TAU-Robotics/ArduMotorControl/Photos/20200909_112209.jpg

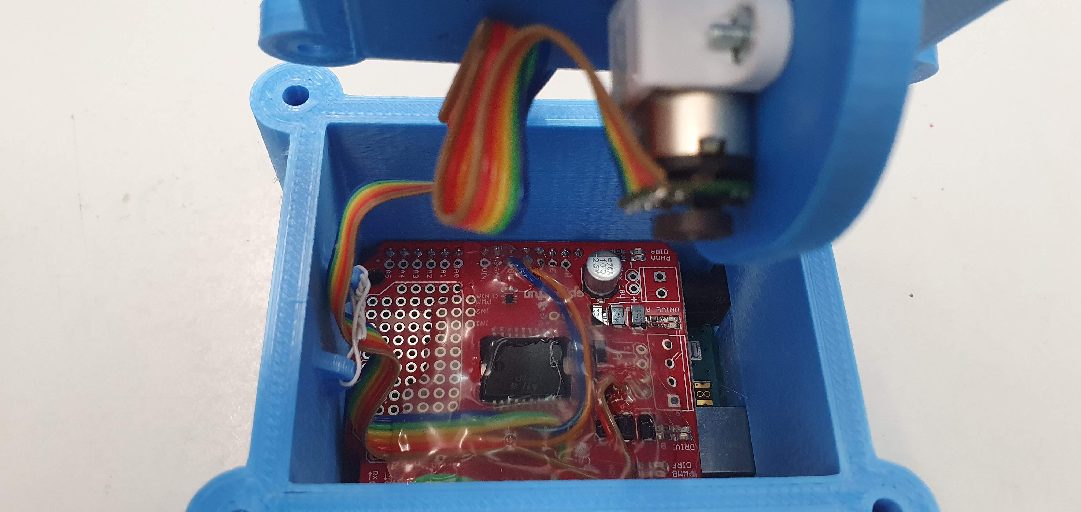
Photos/20200909_112209.jpg
