TAU-Robotics/ArduMotorControl/Photos/20200909_134615.jpg

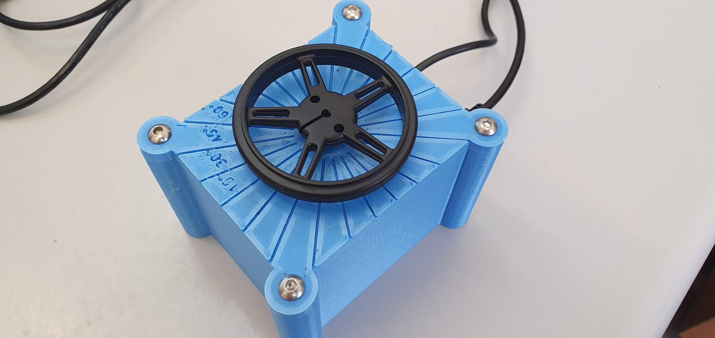
Photos/20200909_134615.jpg
