TAU-Robotics/ArduMotorControl/Photos/20210624_130810.jpg

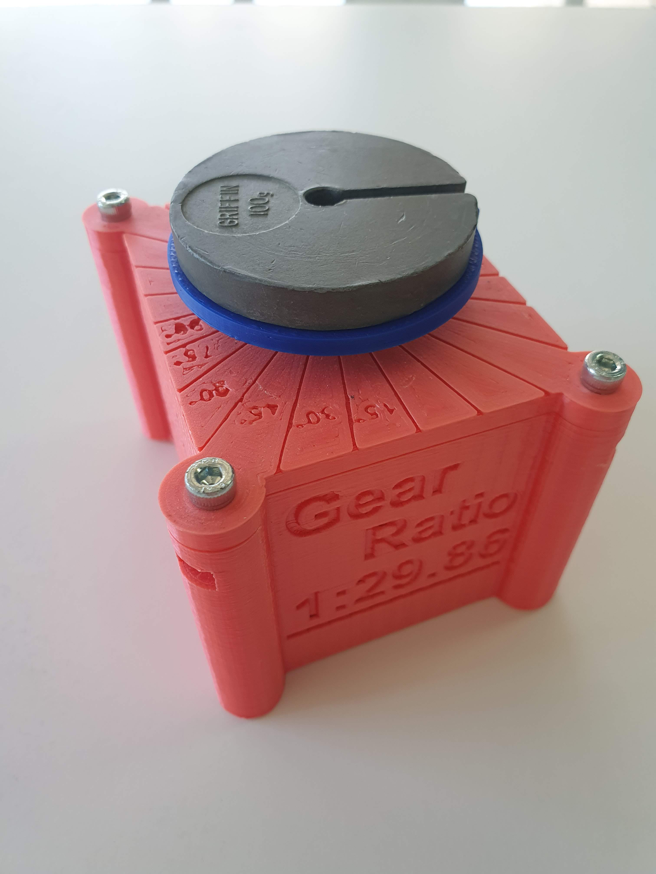
Photos/20210624_130810.jpg
